VolumanXR/volumetric-capture-system/src/utils/pi_config.txt

sudo apt-get install -y python3-picamera2 libcamera-apps libcamera-dev
sudo apt install python3-flask
sudo apt install python3-picamera2
sudo apt install python3-opencv
sudo apt install python3-psutil
sudo apt install python3-numpy

sudo apt update
sudo apt -y upgrade
sudo apt install -y python3-picamera2 libcamera-apps libcamera-dev python3-libcamera libcamera-tools python3-flask python3-opencv python3-psutil python3-numpy
sudo apt install -y python3-netifaces openssh-client

cd voluman/camera/v08/

cd voluman/test01

python3 remote_camera_controller.py

python3 remote_sm.py

python3 remote_transfer.py


sudo apt install python3-zmq

sudo apt install python3-netifaces

sudo apt install -y python3-pip python3-picamera2 libcamera-apps libcamera-dev python3-libcamera libcamera-tools python3-flask python3-opencv python3-psutil python3-numpy python3-netifaces openssh-client python3-zmq
